jpk75/Wordclock/sw/WordClock/src/stringex.cpp

#include "stringex.h"

int StringEx::StringSplit(const String& sInput, char cDelim, String sParams[], int iMaxParams)
{
    int iParamCount = 0;
    int iPosDelim, iPosStart = 0;

    do {
        // Searching the delimiter using indexOf()
        iPosDelim = sInput.indexOf(cDelim,iPosStart);
        if (iPosDelim > (iPosStart+1)) {
            // Adding a new parameter using substring() 
            sParams[iParamCount] = sInput.substring(iPosStart,iPosDelim);
            iParamCount++;
            // Checking the number of parameters
            if (iParamCount >= iMaxParams) {
                return (iParamCount);
            }
            iPosStart = iPosDelim + 1;
        }
    } while (iPosDelim >= 0);
    if (iParamCount < iMaxParams) {
        // Adding the last parameter as the end of the line
        sParams[iParamCount] = sInput.substring(iPosStart);
        iParamCount++;
    }

    return (iParamCount);
}
